fluffy/blinky/hardware/gps_A/production/fixed-pcb.png

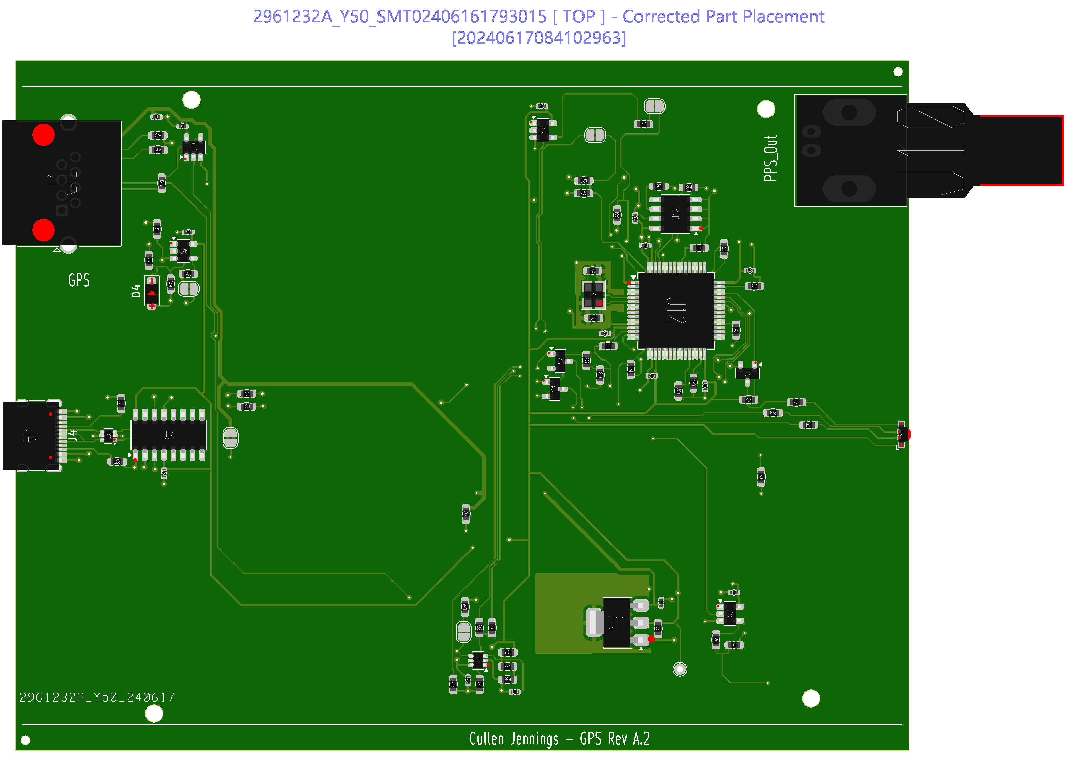
hardware/gps_A/production/fixed-pcb.png
