fluffy/blinky/Core/Src/ltc.c

// SPDX-FileCopyrightText: Copyright (c) 2023 Cullen Jennings
// SPDX-License-Identifier: BSD-2-Clause

//  Descrption of LTC can be found at
//  https://en.wikipedia.org/wiki/Linear_timecode
//  Official specification in SMPTE 12M TODO

#include "ltc.h"

#include <stdio.h>
#include <string.h>

#include "hardware.h"

void LtcTransitionSetClear(LtcTransitionSet* set) {
  set->numTransitions = 0;
  set->nextTransition = 0;
}

void LtcTransitionSetAdd(LtcTransitionSet* set, uint32_t timeUs) {
  if (set->numTransitions >= ltcMaxTransitions) {
    return;
  }
  set->transitionTimeUs[set->numTransitions] = timeUs;
  set->numTransitions++;
}

uint16_t LtcTransitionSetSize(LtcTransitionSet* set) {
  return set->numTransitions;
}

uint32_t LtcTransitionSetDeltaUs(LtcTransitionSet* set, uint16_t i) {
  if ((i < 1) || (i >= set->numTransitions)) {
    return 0;
  }
  return set->transitionTimeUs[i] - set->transitionTimeUs[i - 1];
}

void ltcTimeCodeClear(LtcTimeCode* set) { set->valid = 0; }

void ltcTimeCodeSet(LtcTimeCode* set, uint32_t s, uint32_t us) {
  set->frame = (us * 30l / 1000000l) % 30;
  set->sec = s % 60;
  set->min = (s / 60) % 60;
  set->hour = (s / 3600) % 24;
  set->valid = 1;
}

void ltcTimeCodeSetHMSF(LtcTimeCode* set, uint8_t h, uint8_t m, uint8_t s,
                        uint8_t f) {
  set->frame = f % 30;
  set->sec = s % 60;
  set->min = m % 60;
  set->hour = h % 24;
  set->valid = 1;
}

uint32_t ltcTimeCodeSeconds(LtcTimeCode* set) {
  if (!set->valid) return 0;
  return (uint32_t)(set->sec) + (uint32_t)(set->min) * 60l +
         (uint32_t)(set->hour) * 3600l;
}

uint32_t ltcTimeCodeMicroSeconds(LtcTimeCode* set) {
  if (!set->valid) return 0;
  return (uint32_t)(set->frame) * 1000000l / 30l;
}

uint32_t ltcTimeCodeDisp(LtcTimeCode* set) {
  if (!set->valid) {
    return 0;
  };
  return set->frame + set->sec * 100l + set->min * 10000l +
         set->hour * 1000000l;
}

int ltcTimeCodeIsValid(LtcTimeCode* set) { return set->valid; }

void ltcClear(Ltc* ltc) { ltc->valid = 0; }

uint8_t ltcParity(Ltc* ltc) {
  uint8_t ret = 0;

  for (int i = 0; i < 10; i++) {
    uint8_t data = ltc->bits[i];
    for (int bit = 0; bit <= 8; bit++) {
      if (data & 0x1) {
        ret++;
      }
      data = data >> 1;
    }
  }

  return ret % 2;
}

void ppsEncode(Ltc* ltc, LtcTransitionSet* tSet) {
  LtcTransitionSetClear(tSet);

  uint32_t time = 0;
  LtcTransitionSetAdd(tSet, time);
  time += 5 * 1000;  // 5 ms // TODO - values abovre 5000 do not work
  LtcTransitionSetAdd(tSet, time);
}

void ltcEncode(Ltc* ltc, LtcTransitionSet* tSet, uint8_t fps) {
  LtcTransitionSetClear(tSet);

  uint32_t time = 0;
  // baud rate is 30 fps, 80 bits per frame , two transitions per bit for 1's =
  // 2400 Hz for 1
  uint32_t baud = fps * 80 /* bits per frame */;
  uint32_t zeroInc = 1000000 / baud;  // one time in micro seconds
  uint32_t oneInc = zeroInc / 2;

  LtcTransitionSetAdd(tSet, time);  // first transition at time 0

  for (int i = 0; i < 10; i++) {
    uint16_t data = ltc->bits[i];
    for (uint16_t bit = 0; bit < 8; bit++) {
      // std::cout << " data=" << data << " dataShift=" << (data>>bit) << "
      // bit=" << bit << " "  <<std::endl;
      if ((data >> bit) & 0x1) {
        // encode a one
        time += oneInc;
        LtcTransitionSetAdd(tSet, time);
        time += oneInc;
        LtcTransitionSetAdd(tSet, time);

        // std::cout << "1";
      } else {
        // encode a zero
        time += zeroInc;
        LtcTransitionSetAdd(tSet, time);

        // std::cout << "0";
      }
    }
    // std::cout << "-";
  }

  // std::cout << " totalTime=" << time / 1000 << "ms" << std::endl;
}

int ltcDecode(Ltc* ltc, LtcTransitionSet* tSet, uint8_t fps) {
  uint32_t baud = fps * 80 /* bits per frame */;
  uint32_t zeroInc = 1000000 / baud;  // zero time in micro seconds
  uint32_t oneInc = zeroInc / 2;

  // clear out the data before decoding
  ltc->valid = 0;
  for (int i = 0; i < 10; i++) {
    ltc->bits[i] = 0;
  }

  // decode in reverse direction
  uint8_t bitCount = 7;
  uint8_t byteCount = 9;
  uint16_t setIndex = LtcTransitionSetSize(tSet) - 1;

  uint8_t done = 0;
  while (!done) {
    if (setIndex == 1) {
      // soft fill last bit if missing
      if ((byteCount == 0) && (bitCount <= 1)) {
        if (ltcParity(ltc) == 1) {  // TODO is this correct ???
          ltc->bits[0] |= (1 << 0);
        }

        done = 1;
      } else {
        // std::cout << "not enough transitions" << std::endl;
#if 0
        char buffer[100];
        snprintf(buffer, sizeof(buffer), "BAD LTC not enough transitions at %d %d\r\n",
                 byteCount, bitCount  );
        HAL_UART_Transmit(&hUartDebug, (uint8_t *)buffer, strlen(buffer), 1000);
#endif

        return -1;
      }
    }

    uint32_t delta = LtcTransitionSetDeltaUs(tSet, setIndex);

    if ((delta > zeroInc - 50) && (delta < zeroInc + 50)) {
      // found a zero
      // std::cout << "0";
      setIndex--;
    } else if ((delta > oneInc - 50) && (delta < oneInc + 50)) {
      // found a start of 1
      if (setIndex < 1) {
        // std::cout << "not enough transitions 2nd half of one" << std::endl;
        return -2;
      }
      uint32_t delta2 = LtcTransitionSetDeltaUs(tSet, setIndex - 1);
      if ((delta2 > oneInc - 50) && (delta2 < oneInc + 50)) {
        // found a 1
        // std::cout << "1";

        ltc->bits[byteCount] |= (1 << bitCount);
      } else {
        // std::cout << "  2nd half 1 missing" << std::endl;
        return -3;
      }
      setIndex -= 2;
    } else {
      // std::cout << "  bad delta=" << delta << " at setIndex=" <<
      // (int)setIndex << std::endl;
#if 0  // TODO remove
      char buffer[100];
      snprintf(buffer, sizeof(buffer), "BAD LTC DELTA %lu at index %d\r\n",
               delta, setIndex);
      HAL_UART_Transmit(&hUartDebug, (uint8_t*)buffer, strlen(buffer), 1000);
#endif

      return -4;
    }

    if (bitCount == 0) {
      bitCount = 7;
      if (byteCount == 0) {
        done = 1;
      } else {
        byteCount--;
        // std::cout << "-";
      }
    } else {
      bitCount--;
    }

    if ((byteCount == 7) && (bitCount == 7)) {
      if (ltc->bits[8] != 0xFC) {
        // std::cout << " bad sync1" << std::endl;
        return -5;
      }
    }

    if ((byteCount == 8) && (bitCount == 7)) {
      if (ltc->bits[9] != 0xBF) {
        // std::cout << " bad sync2" << std::endl;
        return -6;
      }
    }
  }

  if (ltcParity(ltc) != 0) {
    // std::cout << " bad parity" << std::endl;
    return -7;
  }
  ltc->valid = 1;

  return 0;
}

void ltcSet(Ltc* ltc, LtcTimeCode* time) {
  ltc->bits[0] = time->frame % 10;
  ltc->bits[1] = time->frame / 10;
  ltc->bits[2] = time->sec % 10;
  ltc->bits[3] = time->sec / 10;
  ltc->bits[4] = time->min % 10;
  ltc->bits[5] = time->min / 10;
  ltc->bits[6] = time->hour % 10;
  ltc->bits[7] = time->hour / 10;
  ltc->bits[8] = 0xFC;  // sync1
  ltc->bits[9] = 0xBF;  // sync2

  if (ltcParity(ltc) == 0) {  // is this correct ??
    // set polarity correction bit
    ltc->bits[3] |= 0x08;
  }

  ltc->valid = 1;
}

void ltcGet(Ltc* ltc, LtcTimeCode* time) {
  time->valid = 0;

  if (!ltc->valid) {
    return;
  }
  if (ltc->bits[8] != 0xFC) {
    return;
  }
  if (ltc->bits[9] != 0xBF) {
    return;
  }

  time->frame = (ltc->bits[1] & 0x03) * 10 + (ltc->bits[0] & 0x0F);
  time->sec = (ltc->bits[3] & 0x07) * 10 + (ltc->bits[2] & 0x0F);
  time->min = (ltc->bits[5] & 0x07) * 10 + (ltc->bits[4] & 0x0F);
  time->hour = (ltc->bits[7] & 0x03) * 10 + (ltc->bits[6] & 0x0F);

  time->frame %= 30;
  time->sec %= 60;
  time->min %= 60;
  time->hour %= 24;

  time->valid = 1;
}
