fluffy/blinky/Core/Inc/setting.h

// SPDX-FileCopyrightText: Copyright (c) 2023 Cullen Jennings
// SPDX-License-Identifier: BSD-2-Clause

#pragma once

#include <stdbool.h>
#include <stdint.h>

typedef struct {
  bool blinkMute;       // mutes audio outout
  bool blinkBlank;      // causes LED to be off
  bool blinkDispAudio;  // caused audio latency to be displayed on LED

  bool blinkHaveDisplay;

  bool blinkPPS;  // do PPS instead of LTC out output

  uint32_t dataNextSyncOutPhaseUS;
  uint32_t dataCurrentSyncOutPhaseUS;

  uint32_t capture2uSRatioM;
  uint32_t capture2uSRatioN;

} Setting;

extern Setting setting;

void settingInit();
void settingSetup();
