fluffy/blinky/Core/Inc/detect.h

// SPDX-FileCopyrightText: Copyright (c) 2023 Cullen Jennings
// SPDX-License-Identifier: BSD-2-Clause

#pragma once

#include <stdbool.h>
#include <stdint.h>

void detectInit(int cycleLen);
void detectUpdate(uint32_t* pData, int len, bool invert);

void detectUpdateMlp(uint32_t time);
void detectGetMlpTime(uint32_t* timeP, float* valP);
void detectResetMlp();

void detectGetDebug(float* minP, float* maxP, float* avgP, float* lastP);
